alx-1/CajitaAbierta/media/images/chataigne_inspector.png

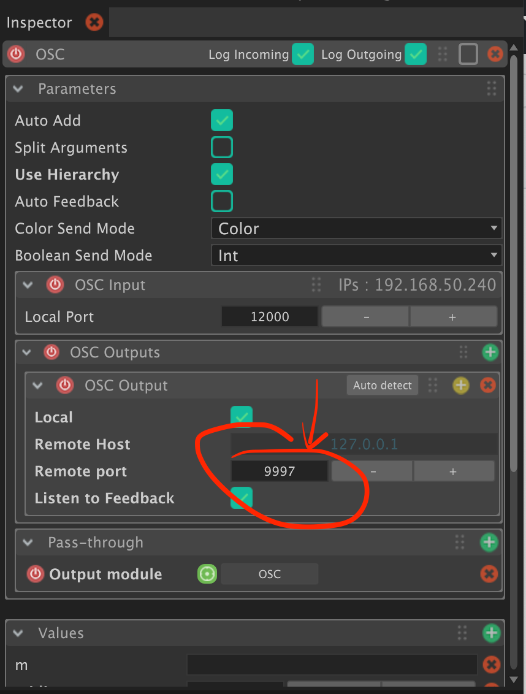
media/images/chataigne_inspector.png
