alx-1/CajitaAbierta/media/images/chataigne_osc.png

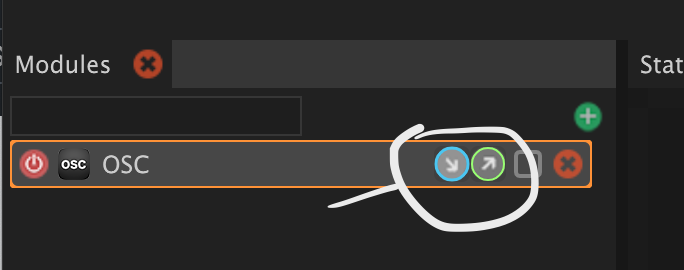
media/images/chataigne_osc.png
