alx-1/CajitaAbierta/media/images/hydra.png

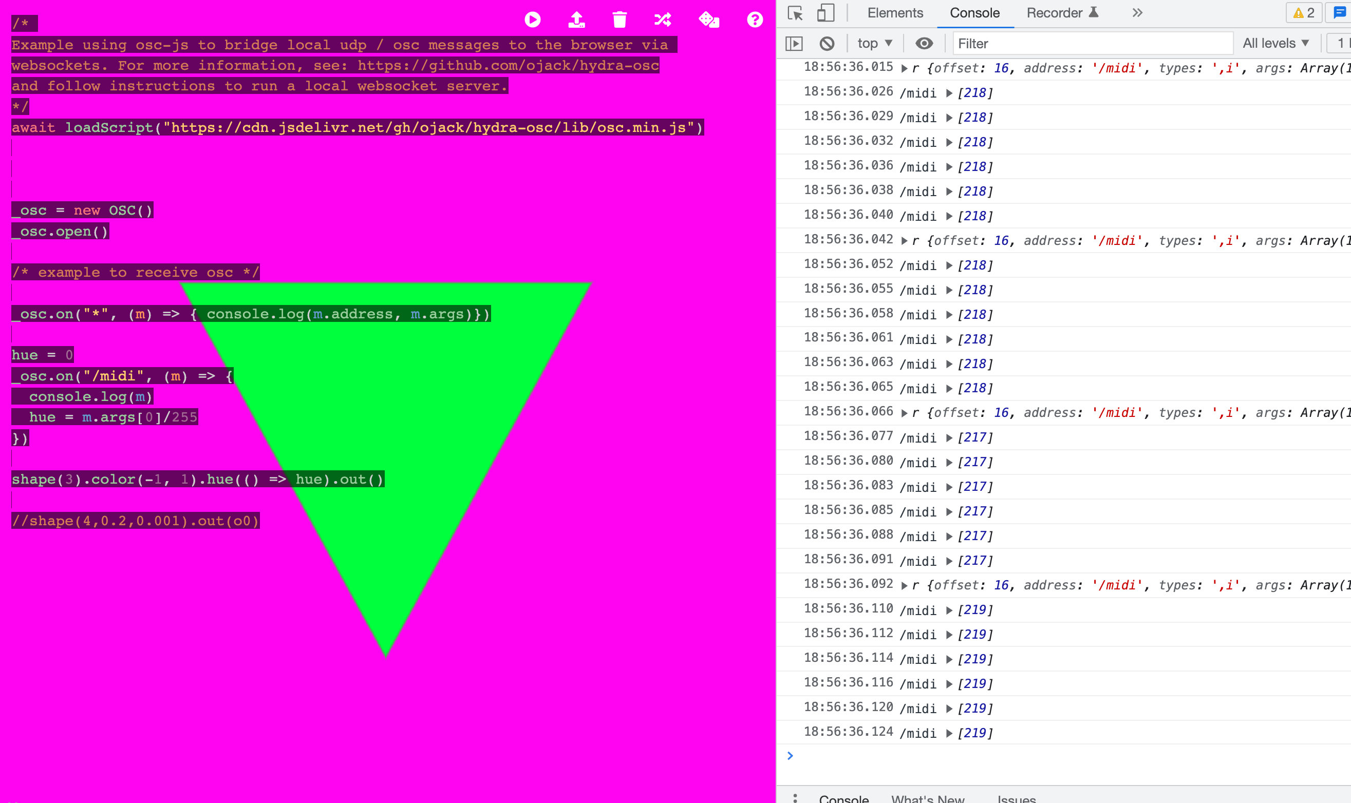
media/images/hydra.png
