alx-1/CajitaAbierta/media/images/login_to_the_esp32.png

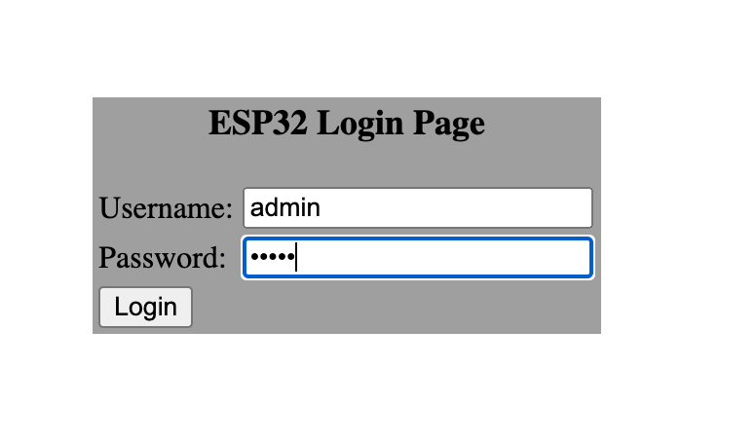
media/images/login_to_the_esp32.png
