alx-1/CajitaAbierta/media/images/open_address_from_browser.png

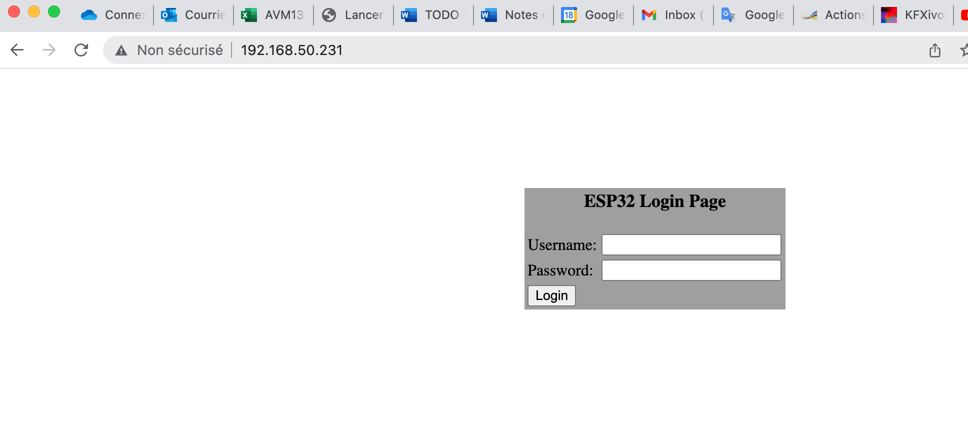
media/images/open_address_from_browser.png
