alx-1/CajitaAbierta/media/images/ossia_osc_config.png

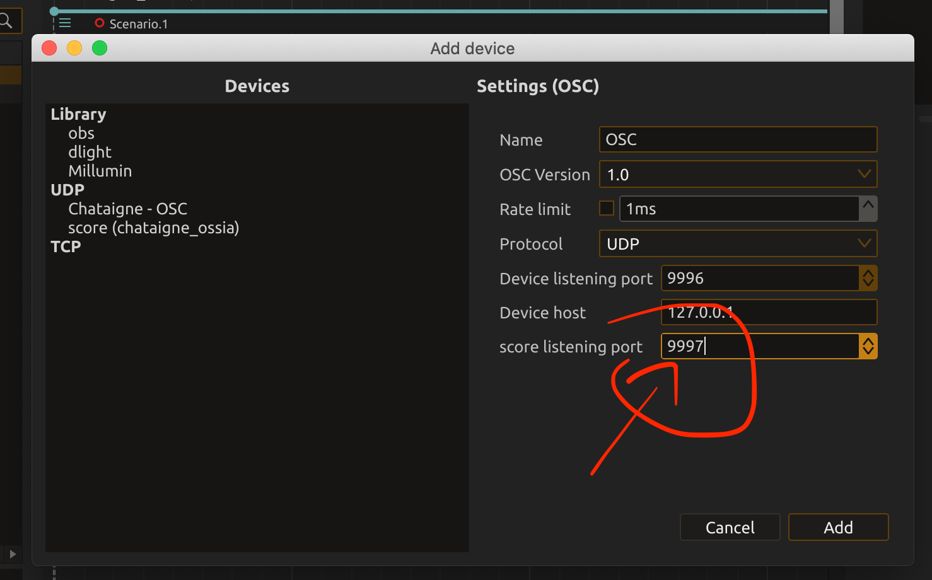
media/images/ossia_osc_config.png
