alx-1/CajitaAbierta/media/images/serial_monitor_connected_to_network.png

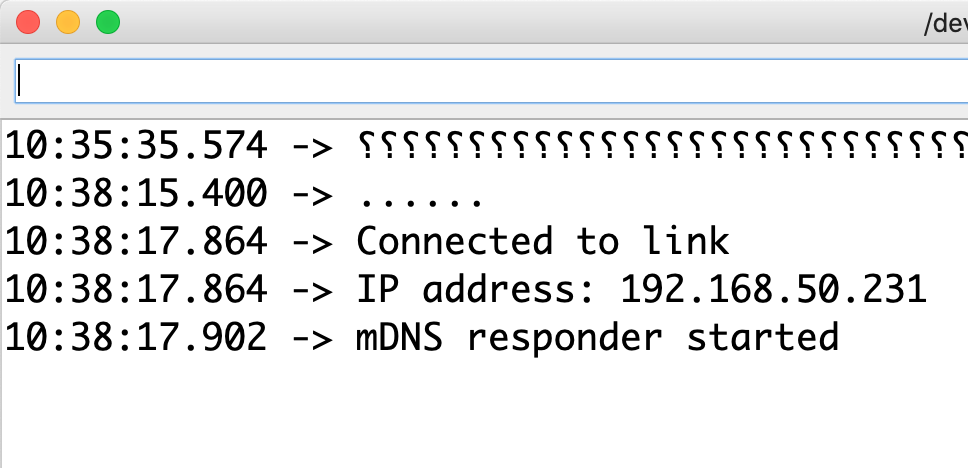
media/images/serial_monitor_connected_to_network.png
