alx-1/CajitaAbierta/media/images/serial_monitor_upload_success.png

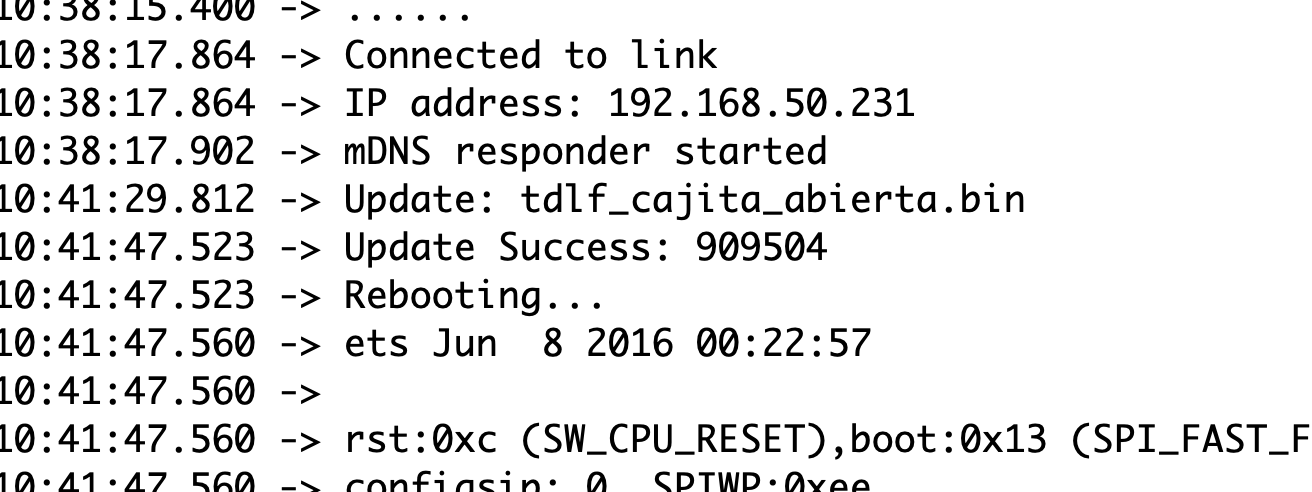
media/images/serial_monitor_upload_success.png
